m-wichmann/pardyBuzz/src/osc_cal.c

#include <avr/interrupt.h>
#include <avr/eeprom.h>
#include "usbdrv.h"
#include "osc_cal.h"

static void calibrateOscillator(void);

static void calibrateOscillator(void)
{
uchar       step = 128;
uchar       trialValue = 0, optimumValue;
int         x, optimumDev, targetValue = (unsigned)(1499 * (double)F_CPU / 10.5e6 + 0.5);
 
    /* do a binary search: */
    do{
        OSCCAL = trialValue + step;
        x = usbMeasureFrameLength();    // proportional to current real frequency
        if(x < targetValue)             // frequency still too low
            trialValue += step;
        step >>= 1;
    }while(step > 0);
    /* We have a precision of +/- 1 for optimum OSCCAL here */
    /* now do a neighborhood search for optimum value */
    optimumValue = trialValue;
    optimumDev = x; // this is certainly far away from optimum
    for(OSCCAL = trialValue - 1; OSCCAL <= trialValue + 1; OSCCAL++){
        x = usbMeasureFrameLength() - targetValue;
        if(x < 0)
            x = -x;
        if(x < optimumDev){
            optimumDev = x;
            optimumValue = OSCCAL;
        }
    }
    OSCCAL = optimumValue;
}
 
void usbEventResetReady(void)
{
    cli();  // usbMeasureFrameLength() counts CPU cycles, so disable interrupts.
    calibrateOscillator();
    sei();
    eeprom_write_byte(0, OSCCAL);   // store the calibrated value in EEPROM
}
